dragon-mobile/solid_state_relays_12v/docs/1670375863793.jpg

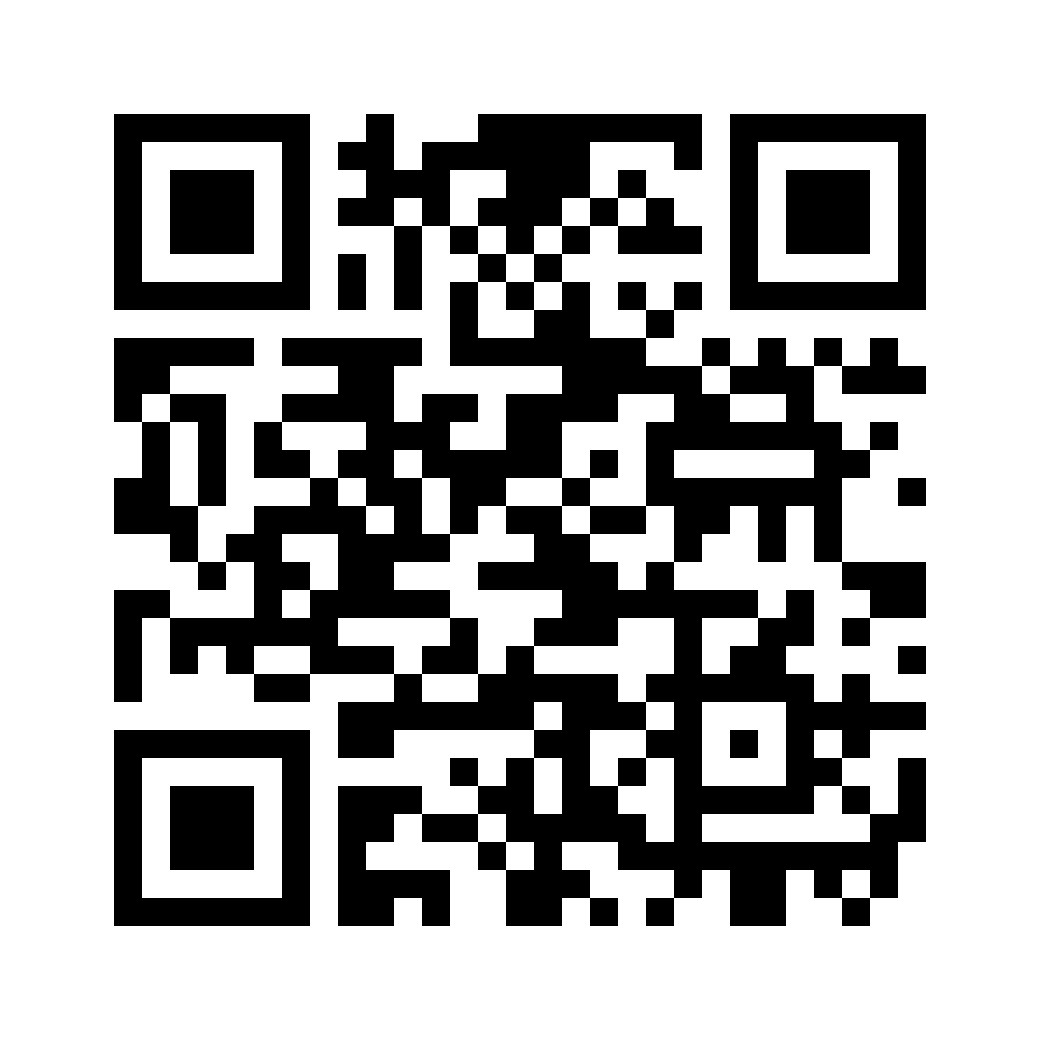
docs/1670375863793.jpg
